dmattox10/ShowStopperLED/Boards/Defiance/BOARD.png

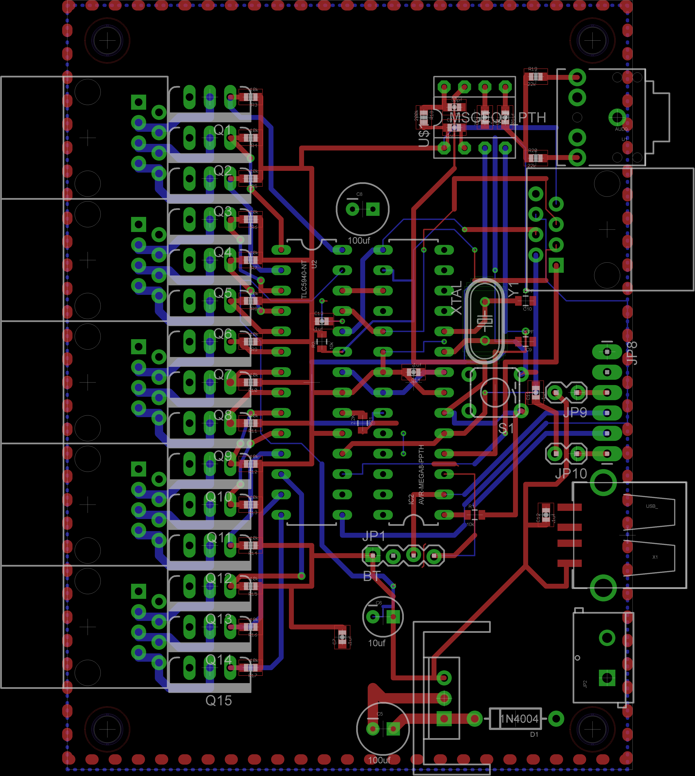
Boards/Defiance/BOARD.png
