dmattox10/ShowStopperLED/Media/02.jpg

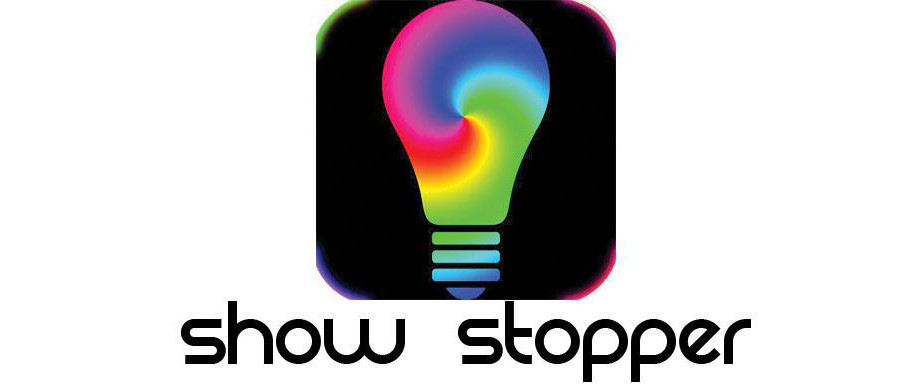
Media/02.jpg
