dmattox10/ShowStopperLED/Media/185096_10151099322512730_103175284_n.jpg

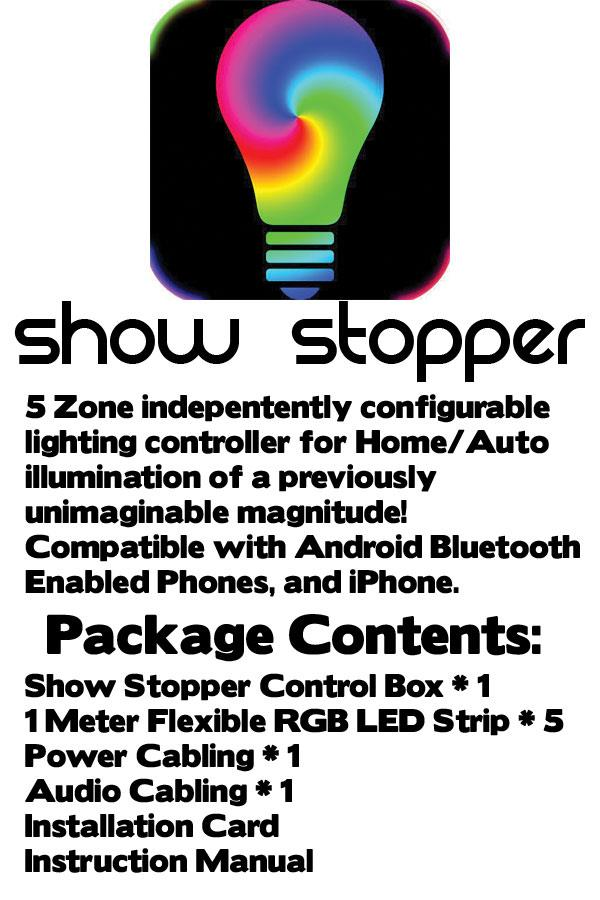
Media/185096_10151099322512730_103175284_n.jpg
