dmattox10/ShowStopperLED/Media/261927_10151097022002730_659508443_n.jpg

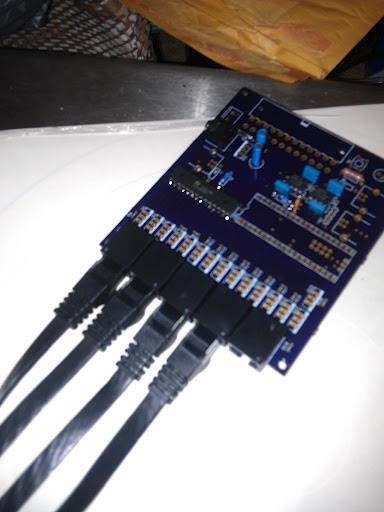
Media/261927_10151097022002730_659508443_n.jpg
