dmattox10/ShowStopperLED/Media/304054_10151097021752730_1785839231_n.jpg

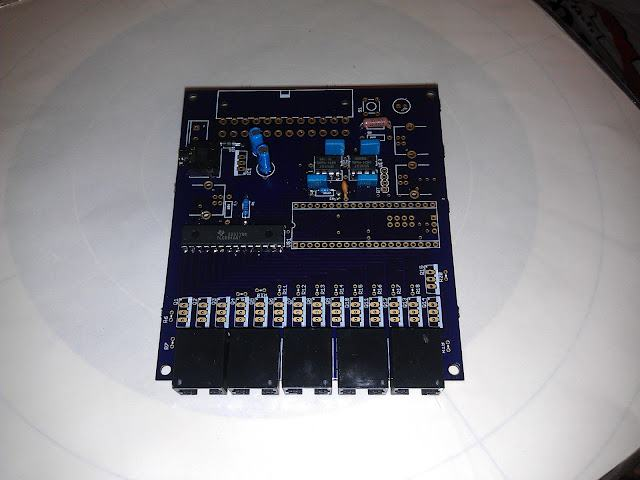
Media/304054_10151097021752730_1785839231_n.jpg
