dmattox10/ShowStopperLED/Media/385657_10151097022147730_1050793818_n.jpg

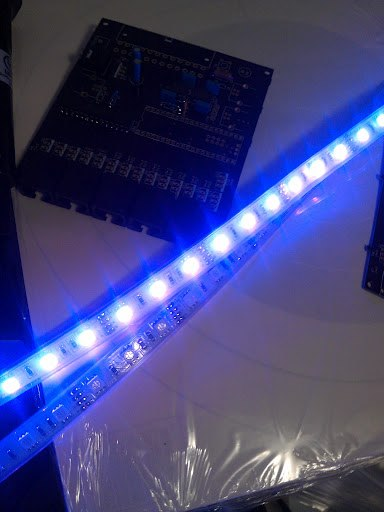
Media/385657_10151097022147730_1050793818_n.jpg
