dmattox10/ShowStopperLED/Media/485743_10151097021932730_1503366523_n.jpg

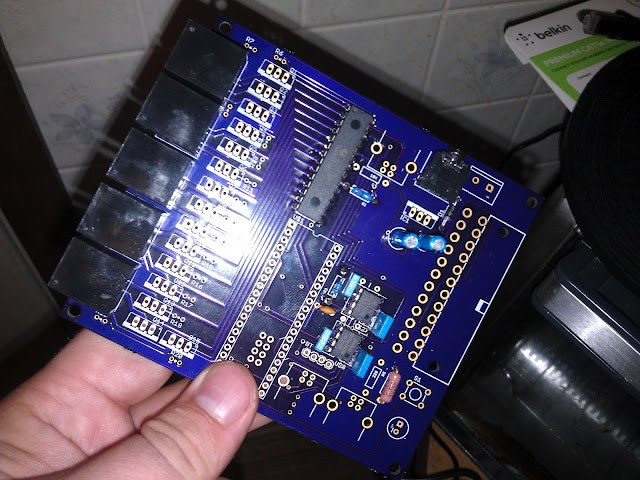
Media/485743_10151097021932730_1503366523_n.jpg
