dmattox10/ShowStopperLED/Media/550454_10151097022372730_347805331_n.jpg

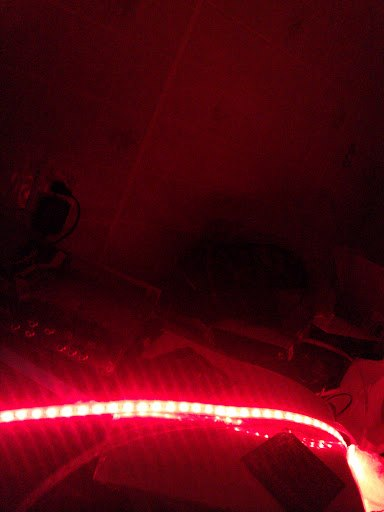
Media/550454_10151097022372730_347805331_n.jpg
