dmattox10/ShowStopperLED/Media/556072_10151097022117730_842343984_n.jpg

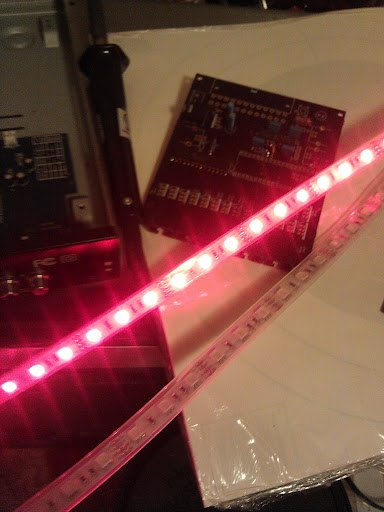
Media/556072_10151097022117730_842343984_n.jpg
