dmattox10/ShowStopperLED/Media/Prototype.png

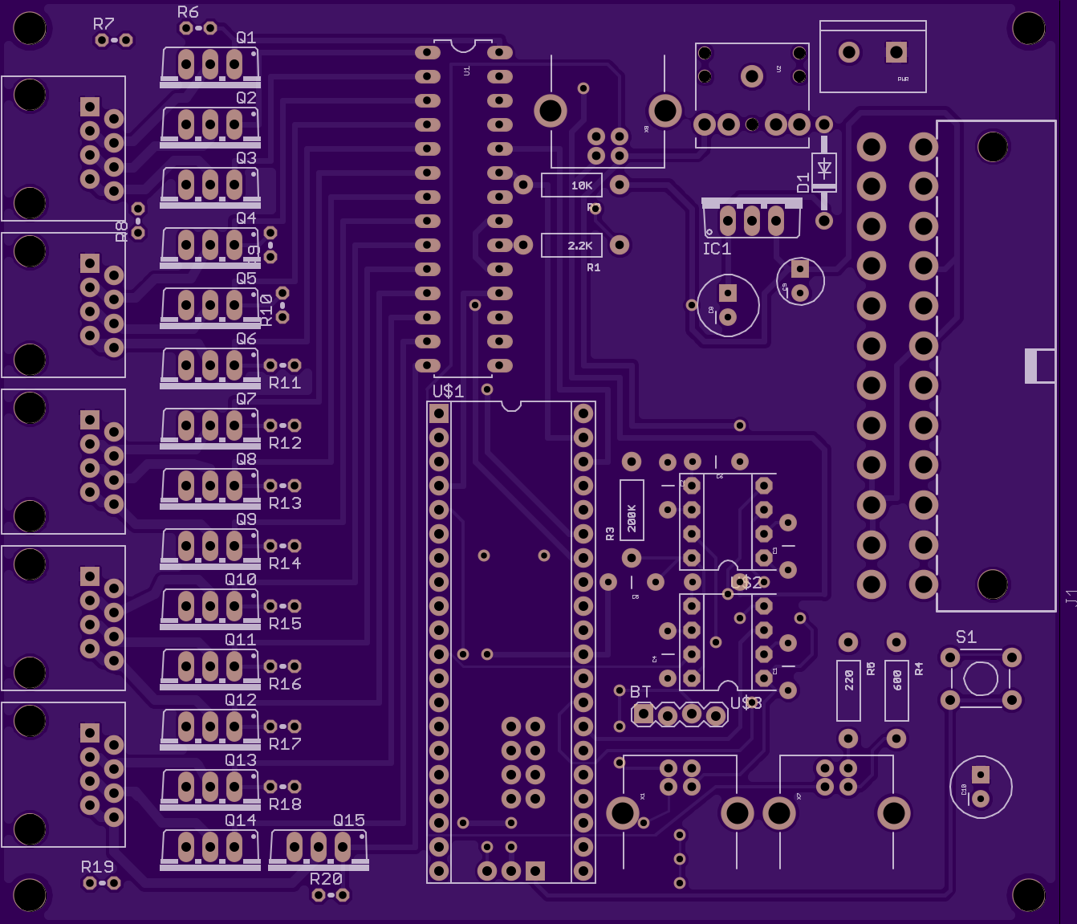
Media/Prototype.png
