dmattox10/ShowStopperLED/Media/red.gif

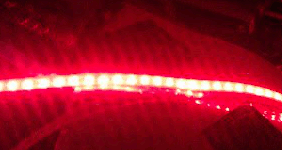
Media/red.gif
