dmattox10/ShowStopperLED/Media/revisionB.png

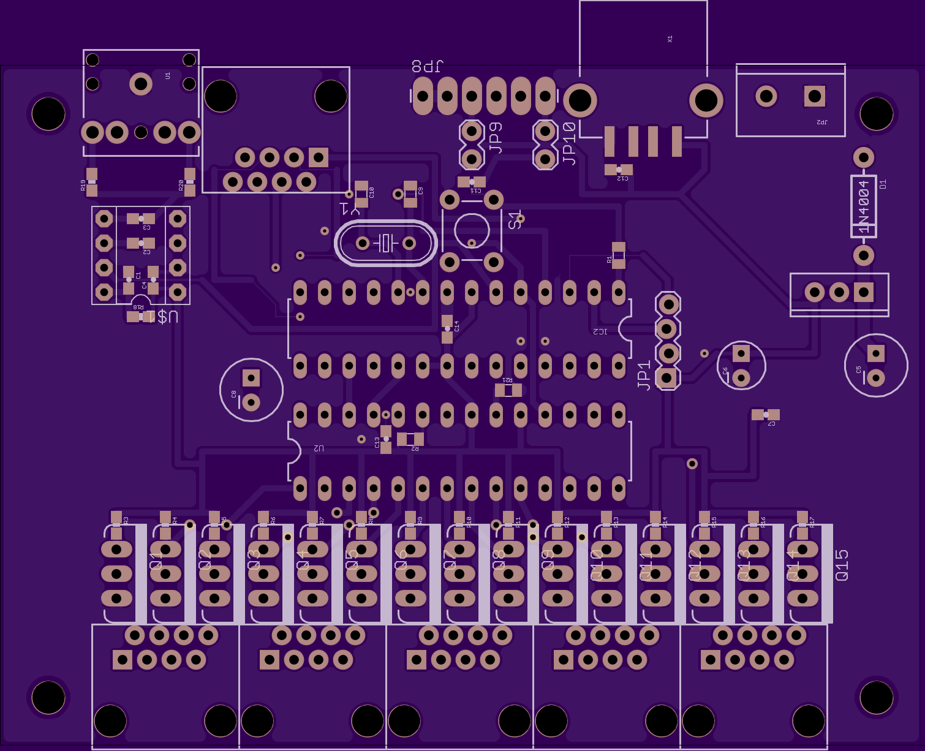
Media/revisionB.png
